NicolasFavero/AsaAutonoma/media/image1.jpeg

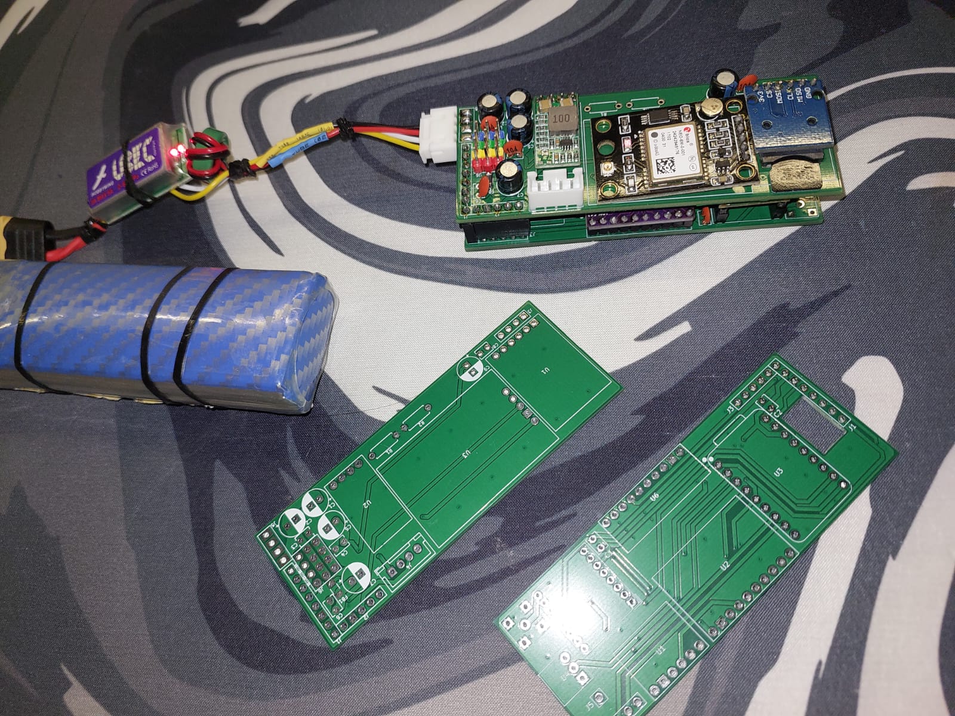
media/image1.jpeg
